cese-dci/tpfinal-loboplateado1203/Componentes/drv8825-1.snapshot.5/Renderings/8825-3.jpg

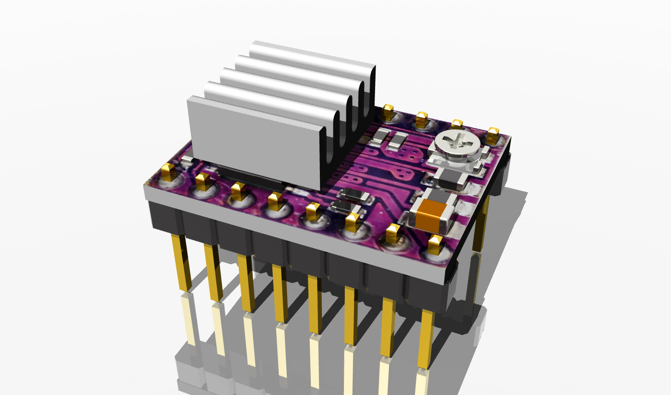
Componentes/drv8825-1.snapshot.5/Renderings/8825-3.jpg
